jp3141/rotary_dialer/Dialer Back.jpg

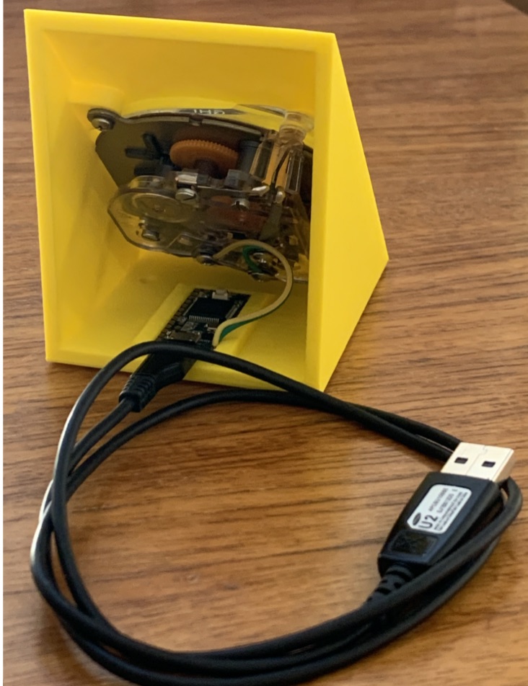
Dialer Back.jpg
